CaptainCookie14/wallet-mp3-player/photos/Screenshot 2026-03-28 175847.png

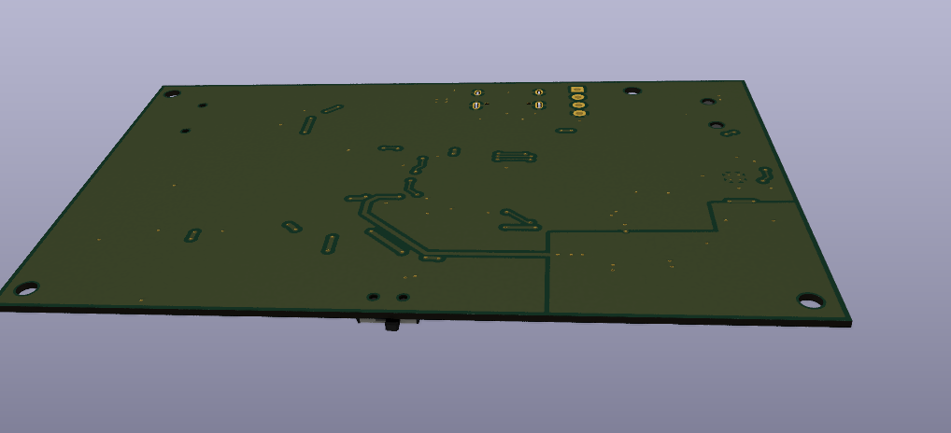
photos/Screenshot 2026-03-28 175847.png
